xioTechnologies/Dub-Siren/Dub-Siren-Firmware/firmware/src/UserInterface/UserInterface.h

/**
 * @file UserInterface.h
 * @author Seb Madgwick
 * @brief User interface module.
 */

#ifndef USER_INTERFACE_H
#define USER_INTERFACE_H

//------------------------------------------------------------------------------
// Function prototypes

void UserInterfaceInitialise();
void UserInterfaceTasks();

#endif

//------------------------------------------------------------------------------
// End of file
