xioTechnologies/Dub-Siren/Dub-Siren-Firmware/firmware/src/FirmwareVersion.h

/**
 * @file FirmwareVersion.h
 * @author Seb Madgwick
 * @brief Firmware version string definition.
 */

#ifndef FIRMWARE_VERSION_H
#define FIRMWARE_VERSION_H

//------------------------------------------------------------------------------
// Definitions

#define FIRMWARE_VERSION "v1.2" " (" __DATE__ " " __TIME__ ")"

#endif

//------------------------------------------------------------------------------
// End of file
