xioTechnologies/Dub-Siren/Dub-Siren-Firmware/firmware/src/UserInterface/DefaultPresets.h

/**
 * @file DefaultPresets.h
 * @author Seb Madgwick
 * @brief Default presets.
 */

#ifndef DEFAULTS_PRESETS_H
#define DEFAULTS_PRESETS_H

//------------------------------------------------------------------------------
// Includes

#include "Synthesiser/Synthesiser.h"

//------------------------------------------------------------------------------
// Variable deceleration

extern const SynthesiserParameters fogHorn;
extern const SynthesiserParameters levelUp;
extern const SynthesiserParameters marioCoin;
extern const SynthesiserParameters bombFalling;
extern const SynthesiserParameters policeSiren;
extern const SynthesiserParameters classicDubSirenLow;
extern const SynthesiserParameters highHat;
extern const SynthesiserParameters classicDubSirenHigh;
extern const SynthesiserParameters bombExploding;
extern const SynthesiserParameters airRaidSiren;

#endif

//------------------------------------------------------------------------------
// End of file
